edbfi/3d-designs/netflix-lettering/docs/images/plates/netflix-letters-colour-swap-a1-mini-plate-2.png

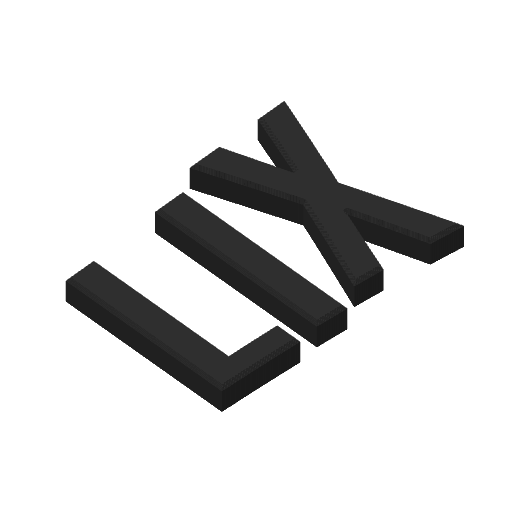
netflix-lettering/docs/images/plates/netflix-letters-colour-swap-a1-mini-plate-2.png
