edbfi/3d-designs/netflix-lettering/docs/images/plates/netflix-plaque-ams-a2l-combo-plate-1.png

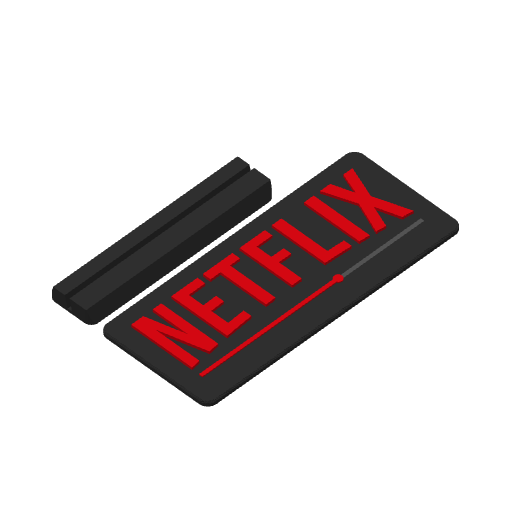
netflix-lettering/docs/images/plates/netflix-plaque-ams-a2l-combo-plate-1.png
