edbfi/3d-designs/netflix-lettering/docs/images/plates/netflix-plaque-single-colour-a1-mini-plate-1.png

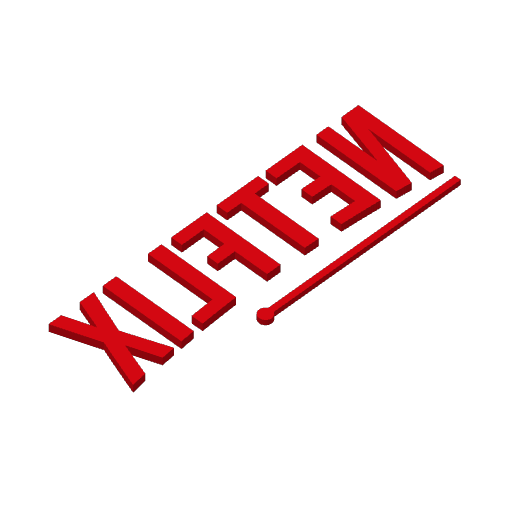
netflix-lettering/docs/images/plates/netflix-plaque-single-colour-a1-mini-plate-1.png
