edbfi/3d-designs/netflix-lettering/docs/images/plates/netflix-stand-ams-a1-mini-plate-1.png

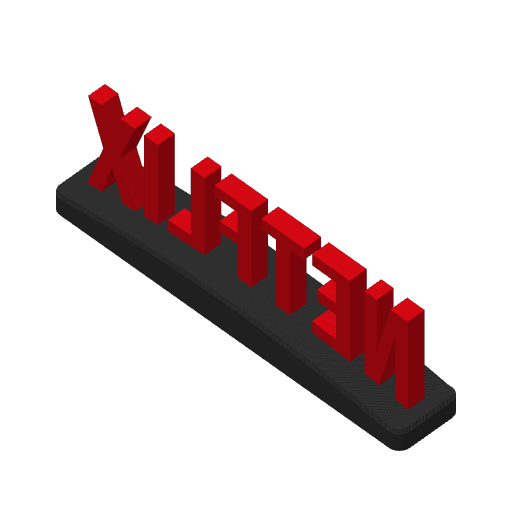
netflix-lettering/docs/images/plates/netflix-stand-ams-a1-mini-plate-1.png
