edbfi/3d-designs/netflix-lettering/docs/images/plates/serier-plaque-ams-a2l-combo-plate-1.png

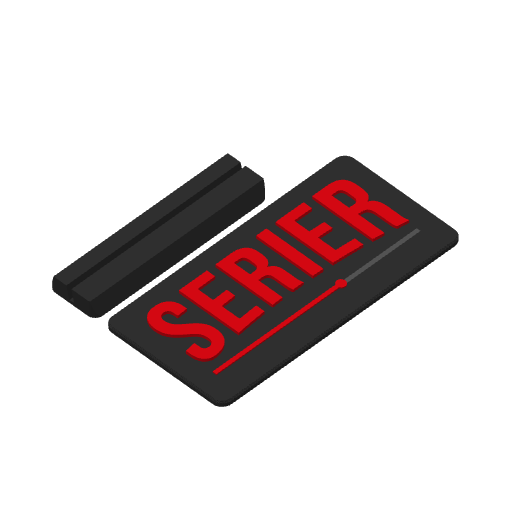
netflix-lettering/docs/images/plates/serier-plaque-ams-a2l-combo-plate-1.png
