edbfi/3d-designs/netflix-lettering/docs/images/plates/serier-stand-ams-a1-mini-plate-1.png

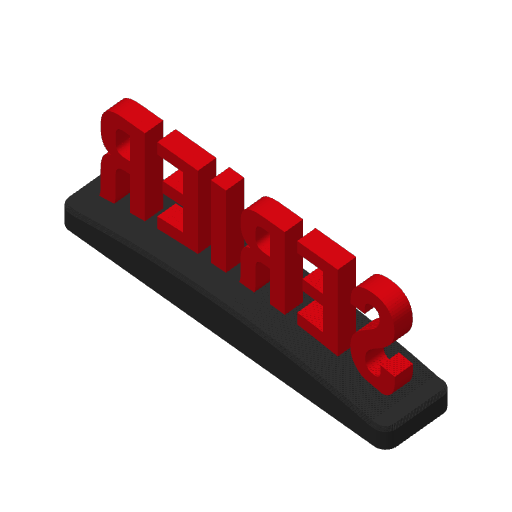
netflix-lettering/docs/images/plates/serier-stand-ams-a1-mini-plate-1.png
