edbfi/3d-designs/netflix-lettering/print-files/single-colour/a1-mini/netflix-plaque-single-colour-a1-mini.3mf

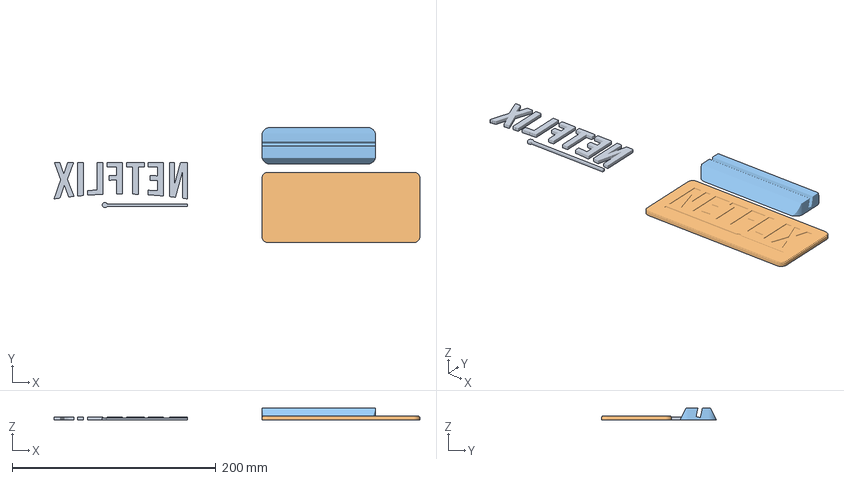
[picture p37: CAD file, 2026-09-29]
netflix-lettering/print-files/single-colour/a1-mini/netflix-plaque-single-colour-a1-mini.3mf
359.2 x 113.0 x 12.0 mm
NETFLIX Red pieces
NETFLIX Plaque
NETFLIX Plaque stand
