edbfi/3d-designs/netflix-lettering/print-files/ams/a1-mini/netflix-stand-ams-a1-mini.3mf

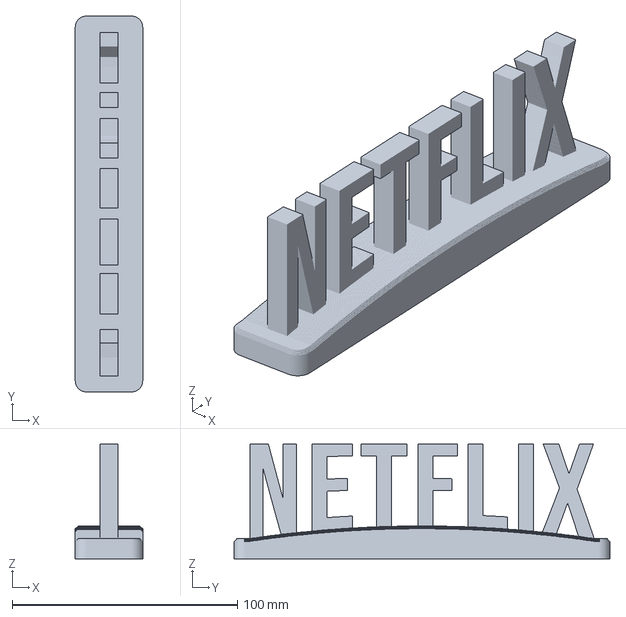
[picture p38: CAD file, 2026-09-29]
netflix-lettering/print-files/ams/a1-mini/netflix-stand-ams-a1-mini.3mf
30.0 x 167.1 x 51.0 mm
