edbfi/3d-designs/netflix-lettering/print-files/ams/a2l-combo/serier-plaque-ams-a2l-combo.3mf

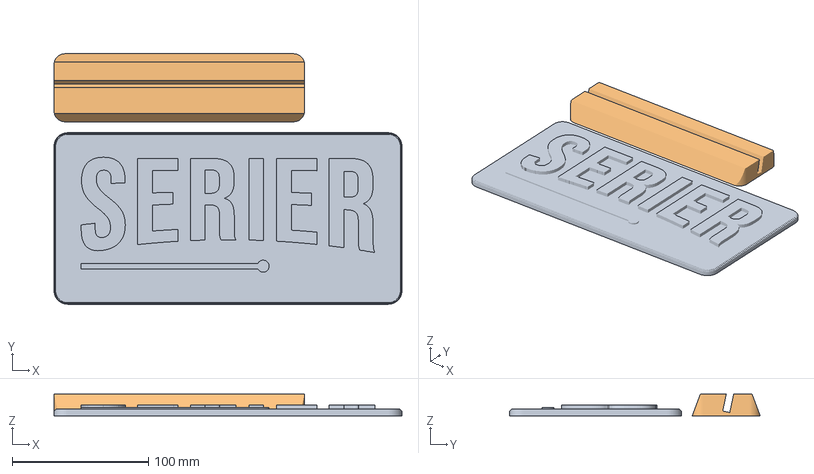
[picture p39: CAD file, 2026-09-29]
netflix-lettering/print-files/ams/a2l-combo/serier-plaque-ams-a2l-combo.3mf
255.6 x 184.0 x 16.0 mm
SERIER Plaque
SERIER Plaque stand
