edbfi/3d-designs/netflix-lettering/print-files/colour-swap/a1-mini/serier-stand-colour-swap-a1-mini.3mf

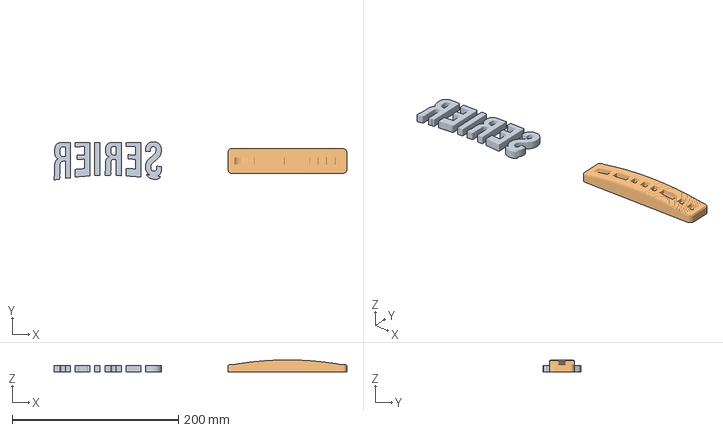
[picture p40: CAD file, 2026-09-29]
netflix-lettering/print-files/colour-swap/a1-mini/serier-stand-colour-swap-a1-mini.3mf
352.3 x 46.0 x 14.6 mm
SERIER Letters
SERIER Plinth
