edbfi/3d-designs/netflix-lettering/print-files/ams/a1-mini/serier-letters-ams-a1-mini.3mf

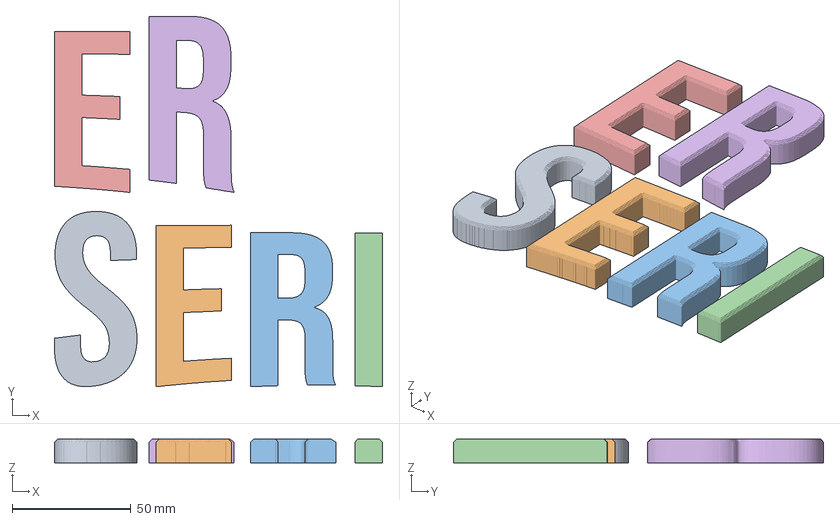
[picture p41: CAD file, 2026-09-29]
netflix-lettering/print-files/ams/a1-mini/serier-letters-ams-a1-mini.3mf
137.8 x 155.6 x 10.0 mm
SERIER Letter 1 S
SERIER Letter 2 E
SERIER Letter 3 R
SERIER Letter 4 I
SERIER Letter 5 E
SERIER Letter 6 R
