edbfi/3d-designs/netflix-lettering/print-files/ams/a2l-combo/netflix-letters-ams-a2l-combo.3mf

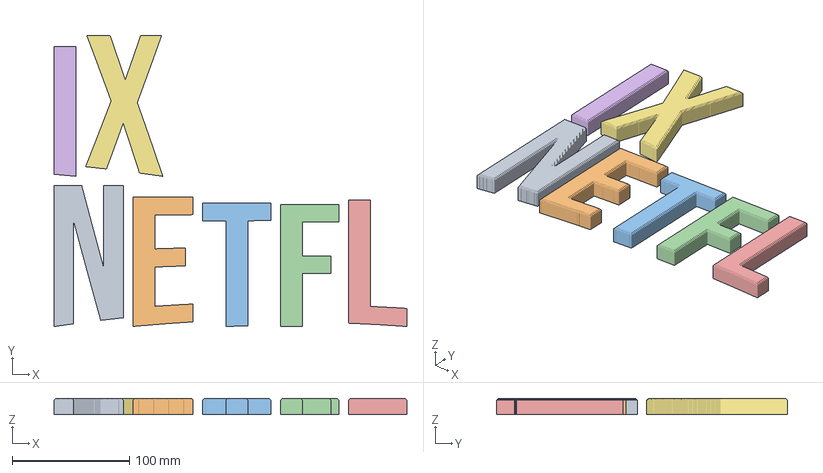
[picture p42: CAD file, 2026-09-29]
netflix-lettering/print-files/ams/a2l-combo/netflix-letters-ams-a2l-combo.3mf
300.7 x 248.0 x 14.0 mm
NETFLIX Letter 1 N
NETFLIX Letter 2 E
NETFLIX Letter 3 T
NETFLIX Letter 4 F
NETFLIX Letter 5 L
NETFLIX Letter 6 I
NETFLIX Letter 7 X
